tooyipjee/Spark-Analyzer/examples/actuator_controller/actuator_controller.ino

/**
 * Spark Analyzer Firmware
 * 
 * This firmware is designed for the Spark Analyzer, a smart home device that integrates 
 * with Matter (formerly known as Project CHIP). It enables the control of lighting 
 * and window systems through USB-C Power Delivery (PD) protocol and Matter over Thread.
 * 
 * Key Features:
 * - Matter integration for controlling On/Off cluster.
 * - USB-C Power Delivery for voltage control and management.
 * - Window control with dedicated pins for open/close status.
 * - LED indicator management.
 * 
 * The firmware sets up the Matter node, initializes USB PD, and controls the GPIO pins 
 * based on Matter cluster updates. It uses the ESP Matter library for the Matter 
 * implementation and handles the USB-C PD with a TCPM driver.
 * 
 * Developed by Jason Too
 * License: MIT
 * 
 * MIT License
 * Copyright (c) 2023 elektroThing
 * 
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
 * THE SOFTWARE IS PROVIDED "AS IS", WITHOUT WARRANTY OF ANY KIND, EXPRESS OR
 * IMPLIED, INCLUDING BUT NOT LIMITED TO THE WARRANTIES OF MERCHANTABILITY,
 * FITNESS FOR A PARTICULAR PURPOSE AND NONINFRINGEMENT. IN NO EVENT SHALL THE
 * AUTHORS OR COPYRIGHT HOLDERS BE LIABLE FOR ANY CLAIM, DAMAGES OR OTHER
 * LIABILITY, WHETHER IN AN ACTION OF CONTRACT, TORT OR OTHERWISE, ARISING FROM,
 * OUT OF OR IN CONNECTION WITH THE SOFTWARE OR THE USE OR OTHER DEALINGS IN THE
 * SOFTWARE.
 */


#include <Arduino.h>
#include <Wire.h>
#include <PD_UFP.h>
#include "Matter.h"
#include <app/server/OnboardingCodesUtil.h>
#include <credentials/examples/DeviceAttestationCredsExample.h>
using namespace chip;
using namespace chip::app::Clusters;
using namespace esp_matter;
using namespace esp_matter::endpoint;

// PD_POWER_OPTION_MAX_5V	
// PD_POWER_OPTION_MAX_9V	
// PD_POWER_OPTION_MAX_12V	
// PD_POWER_OPTION_MAX_15V	
// PD_POWER_OPTION_MAX_20V	
#define VOLTAGE PD_POWER_OPTION_MAX_5V

const int LED_PIN = 3; // Pin 3 is used for LED
const int WINDOW_OPEN_PIN = 8; // Pin 8 for window open status
const int WINDOW_CLOSE_PIN = 9; // Pin 9 for window close status
const int TOGGLE_BUTTON_PIN = 0;
const int DEBOUNCE_DELAY = 500;
int last_toggle;

const uint32_t CLUSTER_ID = OnOff::Id;
const uint32_t ATTRIBUTE_ID = OnOff::Attributes::OnOff::Id;

uint16_t light_endpoint_id = 0;
attribute_t *attribute_ref;

static void on_device_event(const ChipDeviceEvent *event, intptr_t arg) {}
static esp_err_t on_identification(identification::callback_type_t type, uint16_t endpoint_id, uint8_t effect_id, uint8_t effect_variant, void *priv_data) {
  return ESP_OK;
}

static esp_err_t on_attribute_update(attribute::callback_type_t type, uint16_t endpoint_id, uint32_t cluster_id, uint32_t attribute_id, esp_matter_attr_val_t *val, void *priv_data) {
  if (type == attribute::PRE_UPDATE && endpoint_id == light_endpoint_id && cluster_id == CLUSTER_ID && attribute_id == ATTRIBUTE_ID) {
    bool window_status = val->val.b;
    digitalWrite(WINDOW_OPEN_PIN, window_status ? HIGH : LOW);
    digitalWrite(WINDOW_CLOSE_PIN, window_status ? LOW : HIGH);
    digitalWrite(LED_PIN, HIGH); // Ensure pin 3 is always ON
  }
  return ESP_OK;
}
const int usb_pd_int_pin = 10;
PD_UFP_c PD_UFP;

void setup() {
  initializeSerialAndPins();
  initializeUSB_PD();

  // Enable debug logging
  esp_log_level_set("*", ESP_LOG_DEBUG);

  // Setup Matter node
  node::config_t node_config;
  node_t *node = node::create(&node_config, on_attribute_update, on_identification);

  // Setup Light endpoint / cluster / attributes with default values
  on_off_light::config_t light_config;
  light_config.on_off.on_off = false;
  light_config.on_off.lighting.start_up_on_off = false;
  endpoint_t *endpoint = on_off_light::create(node, &light_config, ENDPOINT_FLAG_NONE, NULL);

  // Save on/off attribute reference. It will be used to read attribute value later.
  attribute_ref = attribute::get(cluster::get(endpoint, CLUSTER_ID), ATTRIBUTE_ID);

  // Save generated endpoint id
  light_endpoint_id = endpoint::get_id(endpoint);
  
  // Setup DAC (this is good place to also set custom commission data, passcodes etc.)
  esp_matter::set_custom_dac_provider(chip::Credentials::Examples::GetExampleDACProvider());

  // Start Matter device
  esp_matter::start(on_device_event);

  // Print codes needed to setup Matter device
  PrintOnboardingCodes(chip::RendezvousInformationFlags(chip::RendezvousInformationFlag::kBLE));
  pinMode(WINDOW_OPEN_PIN, OUTPUT);
  pinMode(WINDOW_CLOSE_PIN, OUTPUT);
  pinMode(20, OUTPUT);
  digitalWrite(20, HIGH); // Set pin 3 to HIGH in setup

  digitalWrite(LED_PIN, HIGH); // Set pin 3 to HIGH in setup
}

// Reads light on/off attribute value
esp_matter_attr_val_t get_onoff_attribute_value() {
  esp_matter_attr_val_t onoff_value = esp_matter_invalid(NULL);
  attribute::get_val(attribute_ref, &onoff_value);
  return onoff_value;
}

// Sets light on/off attribute value
void set_onoff_attribute_value(esp_matter_attr_val_t* onoff_value) {
  attribute::update(light_endpoint_id, CLUSTER_ID, ATTRIBUTE_ID, onoff_value);
}

void loop() {
  updateStatus();
   if ((millis() - last_toggle) > DEBOUNCE_DELAY) {
    if (!digitalRead(TOGGLE_BUTTON_PIN)) {
      last_toggle = millis();
      // Read actual on/off value, invert it and set
      esp_matter_attr_val_t onoff_value = get_onoff_attribute_value();
      onoff_value.val.b = !onoff_value.val.b;
      set_onoff_attribute_value(&onoff_value);
    }
  }
}



// Initialize Serial and Pin Modes
void initializeSerialAndPins() {
  Serial.begin(115200);
  Serial.println("Initializing...");

  pinMode(usb_pd_int_pin, INPUT);
  pinMode(LED_PIN, OUTPUT);
  digitalWrite(LED_PIN, HIGH);
}

// Initialize USB Power Delivery
void initializeUSB_PD() {
  Wire.begin(1, 0);
  Wire.setClock(400000);
  PD_UFP.init(usb_pd_int_pin, PD_POWER_OPTION_MAX_20V);

}

// Update status at intervals
void updateStatus() {
  PD_UFP.run();
}
